scottfeldman/closinuf/cad/encoder wheel.FCStd

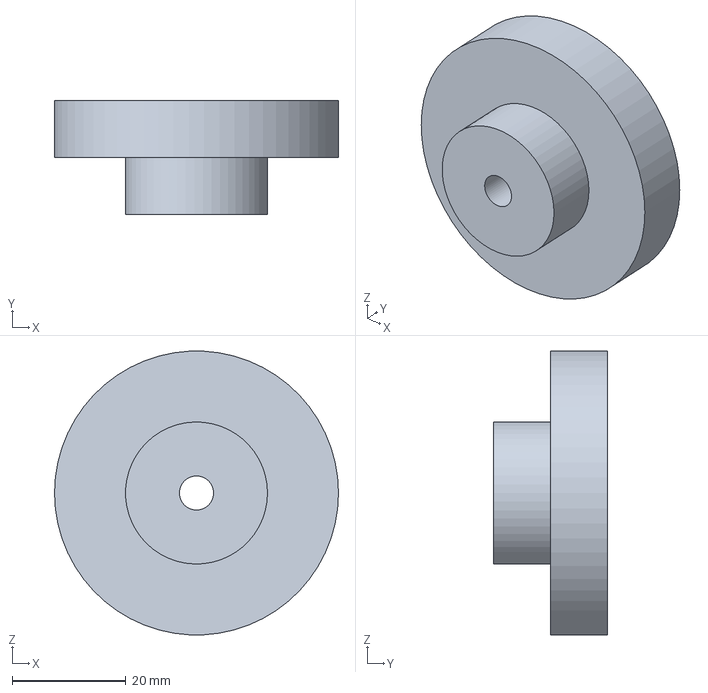
[picture p16: CAD file, 2026-03-28]
cad/encoder wheel.FCStd
50.0 x 20.0 x 49.9 mm
