scottfeldman/closinuf/cad/rotary encoder 600 ppr.FCStd

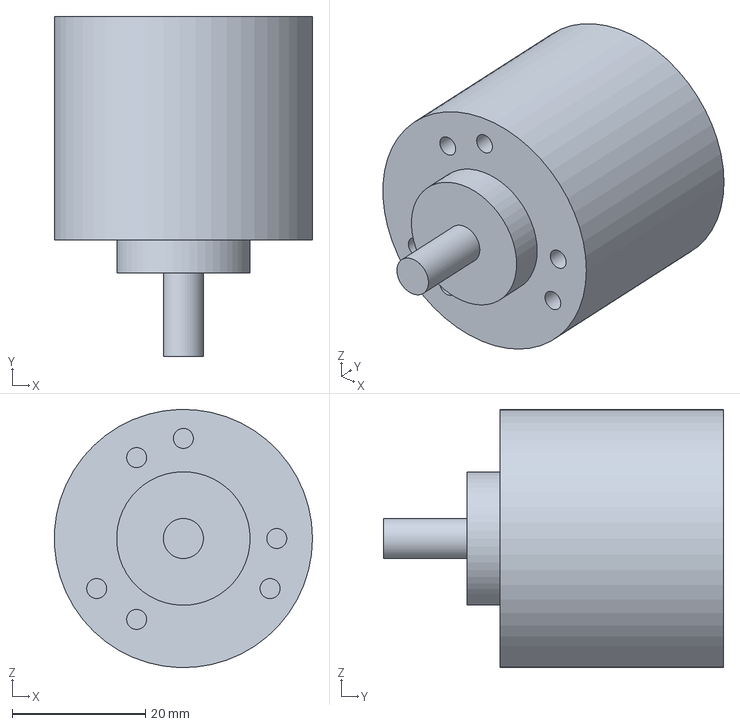
[picture p17: CAD file, 2026-03-28]
cad/rotary encoder 600 ppr.FCStd
38.7 x 51.0 x 38.7 mm
