scottfeldman/closinuf/cad/SBR20 rail stop.FCStd

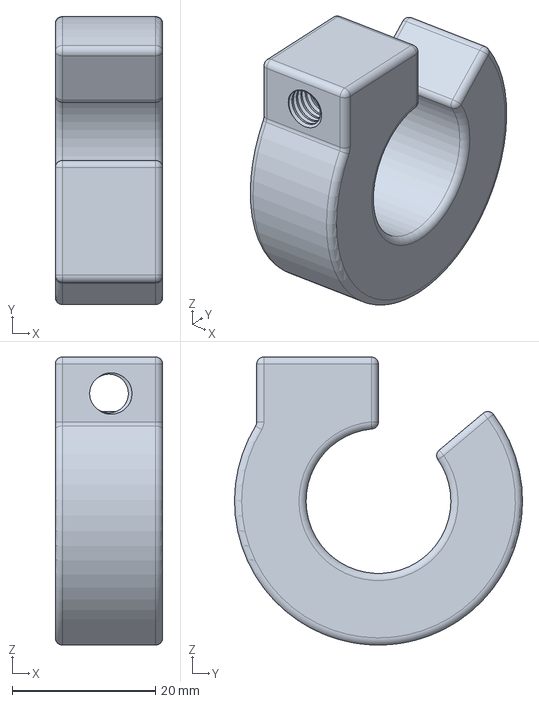
[picture p18: CAD file, 2026-03-28]
cad/SBR20 rail stop.FCStd
15.0 x 40.2 x 40.2 mm
