scottfeldman/closinuf/cad/2x2x0.125 tubing.FCStd

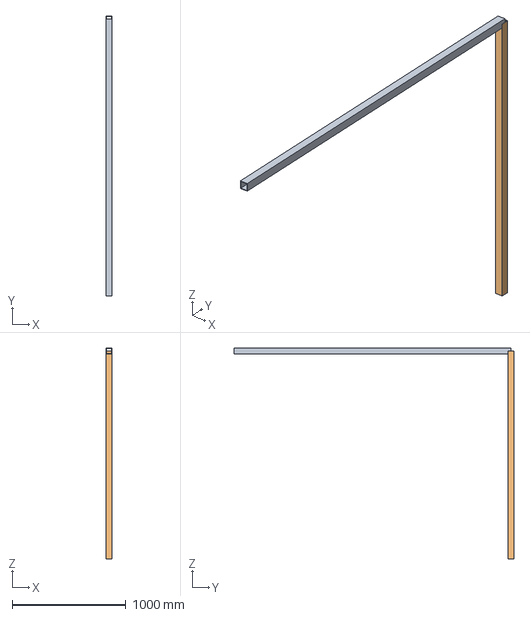
[picture p19: CAD file, 2026-03-28]
cad/2x2x0.125 tubing.FCStd
50.8 x 2463.8 x 1854.2 mm
8' tubing
6' tubing
