scottfeldman/closinuf/cad/2x2 corner.FCStd

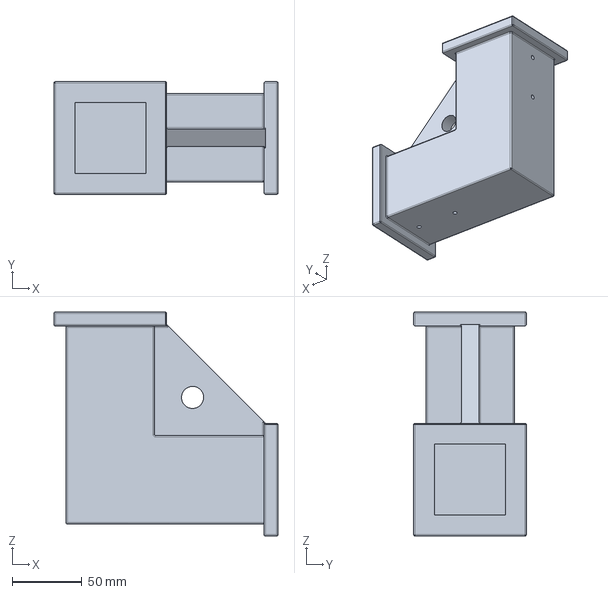
[picture p20: CAD file, 2026-01-30]
cad/2x2 corner.FCStd
161.1 x 81.1 x 161.1 mm
